GrantMaiden/KeyPal/Final/resources/finger_4.png

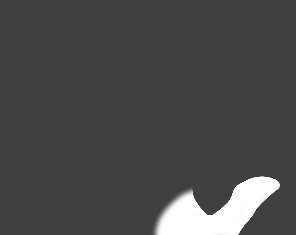
Final/resources/finger_4.png
